iOperator/FRAMpen/software/test.py

# FRAMpen
# This file contains some sample data for testing.

# Use this data for 'data_x', 'data_y', 'data_z'.
sample1_raw_x = [4304, 4304, 4304, 4304, 4304, 4304, 4304, 4304, 4304,
                 4304, 4304, 4304, 4304, 4304, 4304, 4304, 4304, 4304,
                 4304, 4304, 4304, 4309, 4299, 4304, 4304, 4304, 4304,
                 4304, 4304, 4304, 4304, 4304, 4304, 4304, 4304, 4304,
                 4304, 4304, 4304, 4304, 4304, 4304, 4304, 4304, 4304,
                 4304, 4304, 4304, 4304, 4304, 4304, 4304, 4304, 4304,
                 4304, 4303, 4304, 4304, 4304, 4304, 4304, 4304, 4304,
                 4304, 4304, 4304, 4304, 4304, 4304, 4304, 4304, 4304,
                 4304, 4304, 4304, 4304, 4304, 4304, 4304, 4304, 4304,
                 4304, 4304, 4304, 4304, 4304, 4304, 4304, 4304, 4304,
                 4304, 4304, 4304, 4304, 4304, 4302, 4304, 4304, 4304,
                 4304, 4304, 4304, 4304, 4304, 4304, 4304, 4304, 4304,
                 4304, 4304, 4304, 4304, 4304, 4304, 4304, 4304, 4304,
                 4304, 4304, 4304, 4304, 4304, 4304, 4304, 4304, 4304,
                 4304, 4304, 4304, 4304, 4304, 4304, 4304, 4304, 4304,
                 4304, 4304, 4304, 4304, 4304, 4304, 4304, 4304, 4304,
                 4304, 4304, 4304, 4304, 4304, 4304, 4304, 4304, 4304,
                 4304, 4304, 4304, 4304, 4304, 4304, 4304, 4304, 4304,
                 4304, 4304, 4304, 4304, 4304, 4304, 4304, 4304, 4304,
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
                 5296, 5291, 5296, 5296, 5280, 5294, 5296, 5281, 5288,
                 5281, 5289, 5285, 5295, 5292, 5293, 5291, 5281, 5282,
                 5285, 5294, 5295, 5280, 5287, 5289, 5296, 5296, 5288,
                 5286, 5282, 5296, 5288, 5280, 5286, 5289, 5296, 5290,
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
